raspberrypilearning/laser-tripwire/code/fritzing/LDR_true_bb.png

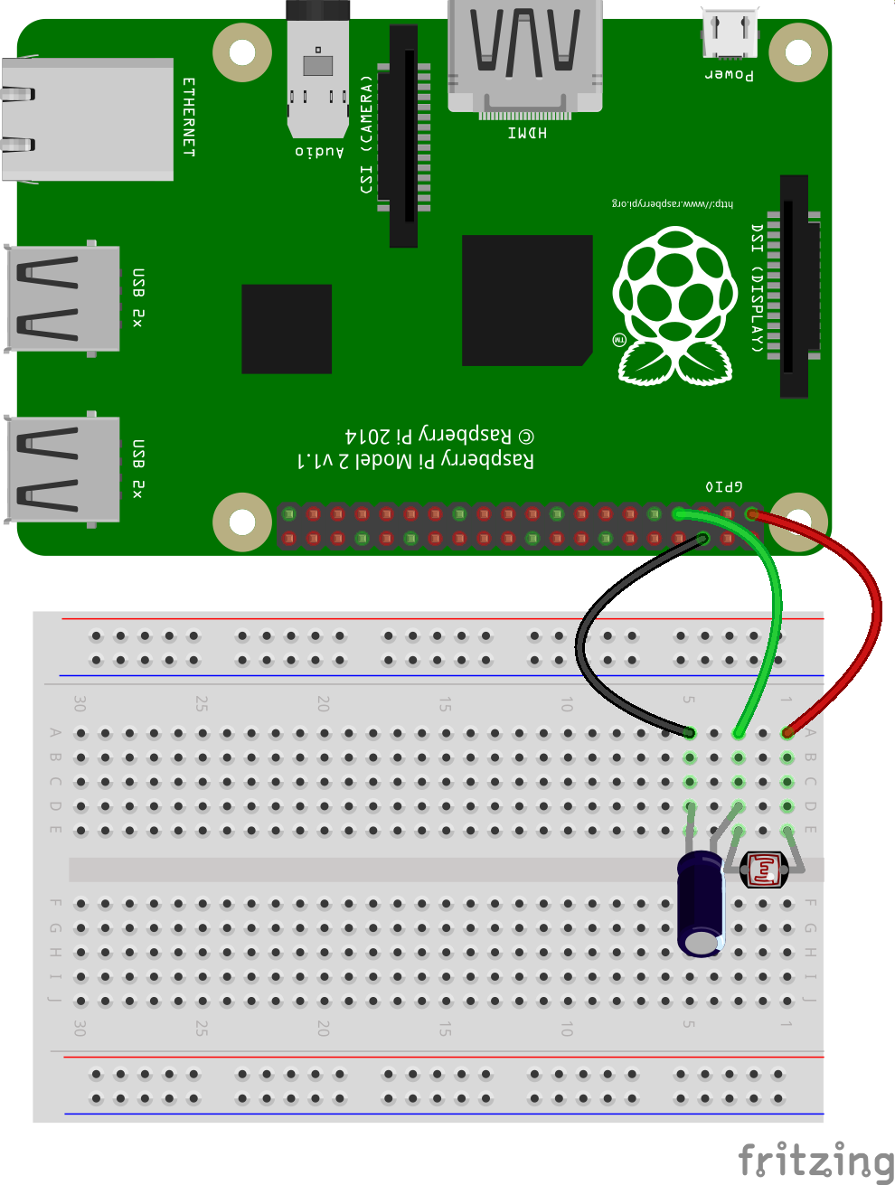
code/fritzing/LDR_true_bb.png
