raspberrypilearning/laser-tripwire/en/images/circuit.png

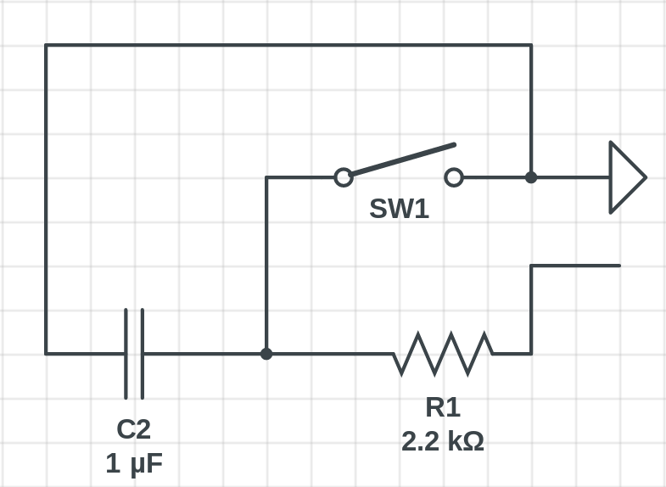
en/images/circuit.png
