raspberrypilearning/laser-tripwire/en/images/LDR_bb.png

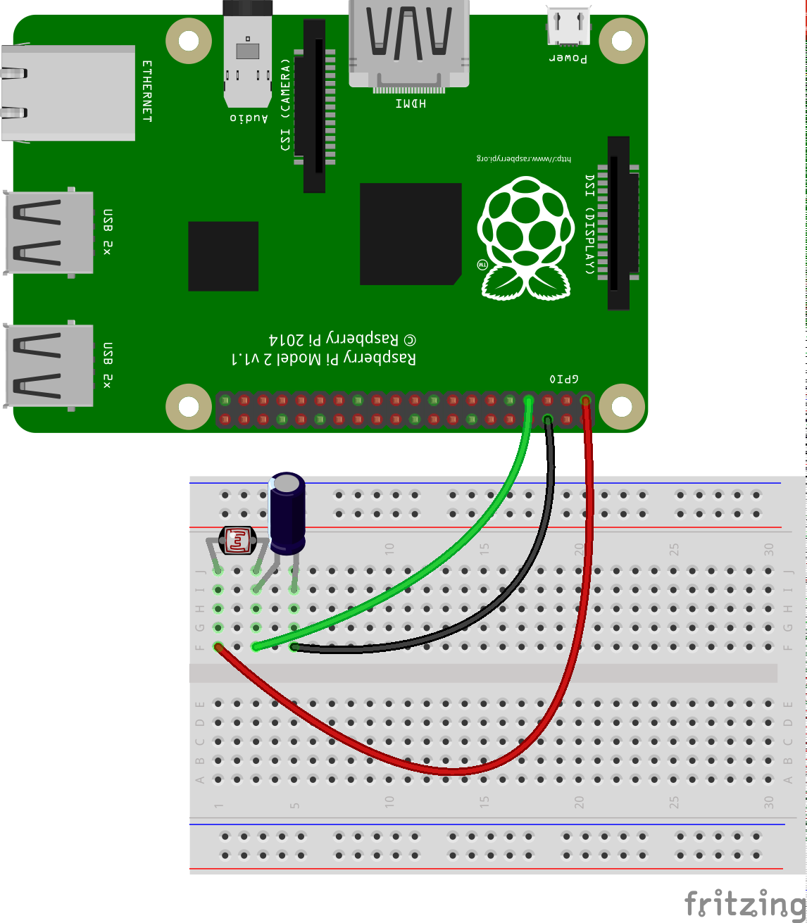
en/images/LDR_bb.png
