raspberrypilearning/laser-tripwire/en/images/LDR_buzzer_bb.png

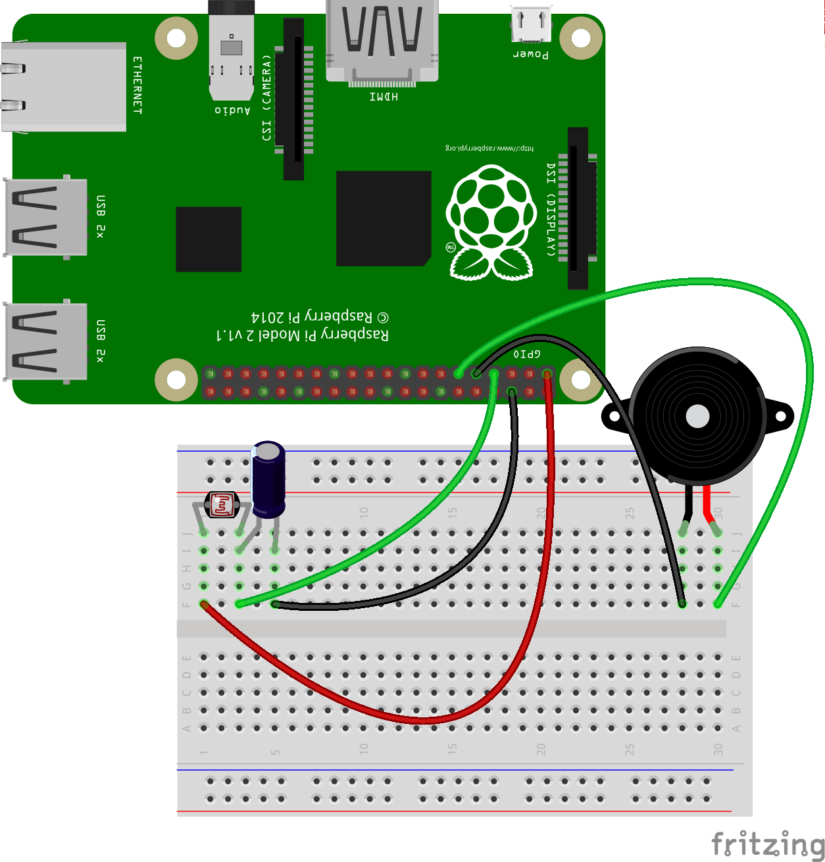
en/images/LDR_buzzer_bb.png
